okyeron/neotrellis-monome/enclosure/flexi-pcb3-1080.jpg

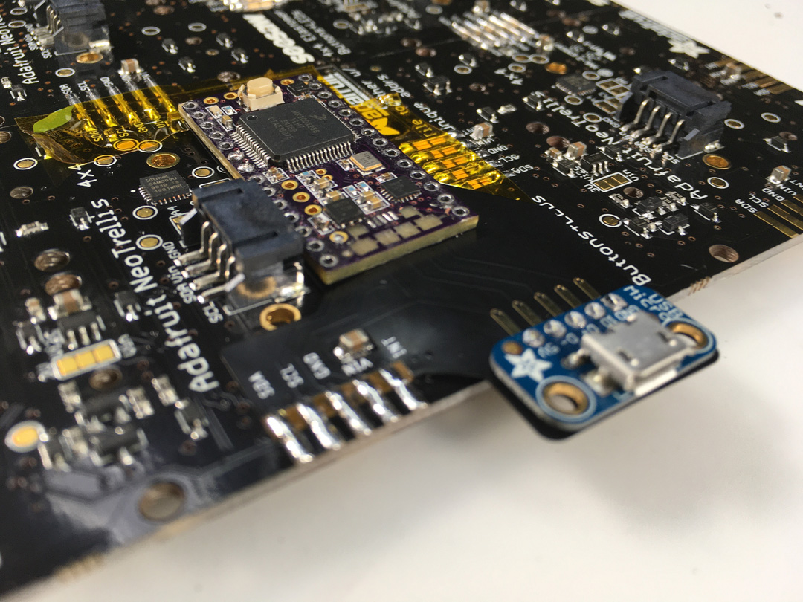
enclosure/flexi-pcb3-1080.jpg
