okyeron/neotrellis-monome/enclosure/IMG_2868.JPG

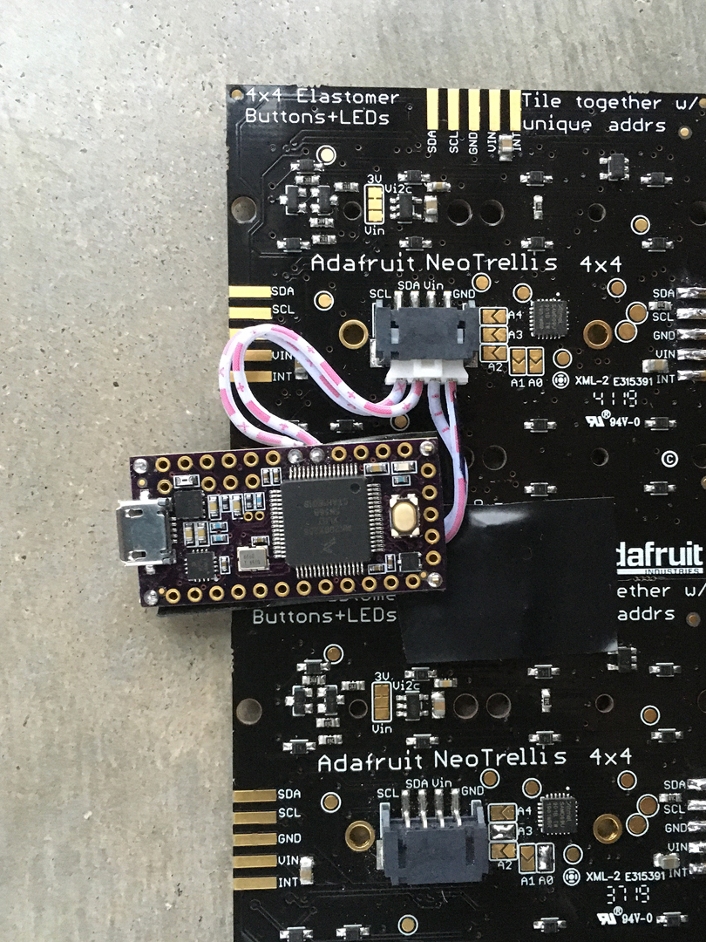
enclosure/IMG_2868.JPG
