okyeron/neotrellis-monome/enclosure/IMG_2871.JPG

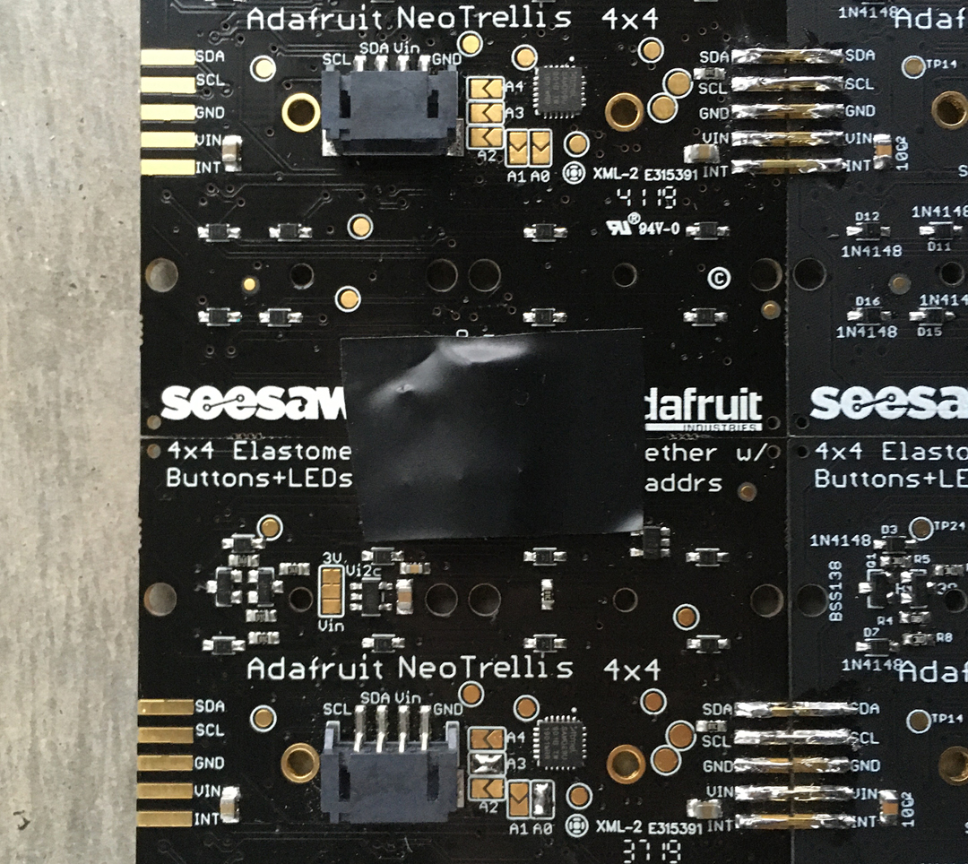
enclosure/IMG_2871.JPG
