okyeron/neotrellis-monome/enclosure/IMG_2872.JPG

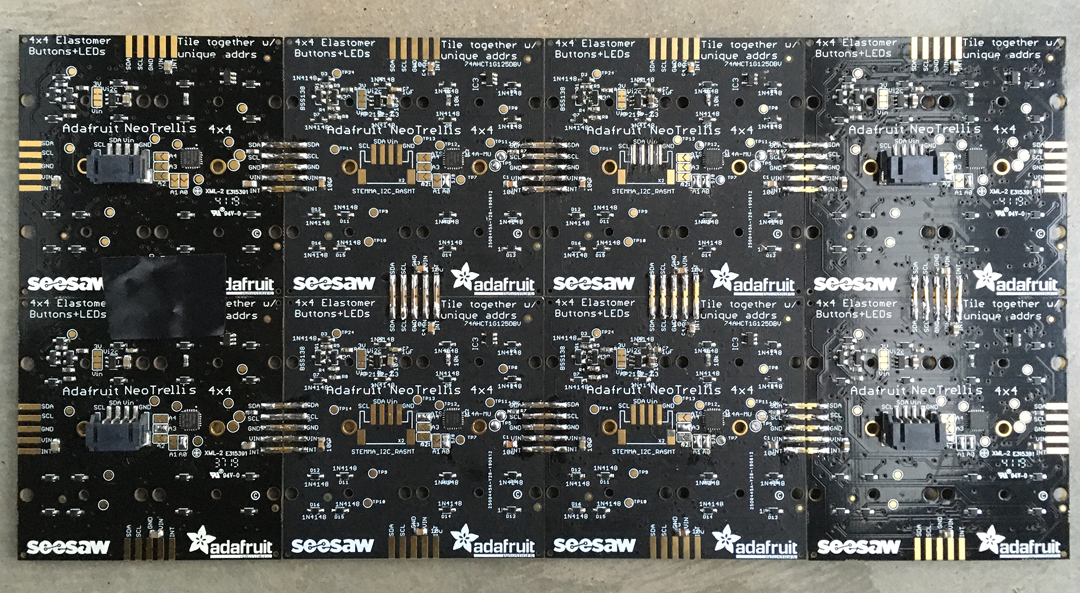
enclosure/IMG_2872.JPG
