okyeron/neotrellis-monome/enclosure/IMG_2873.JPG

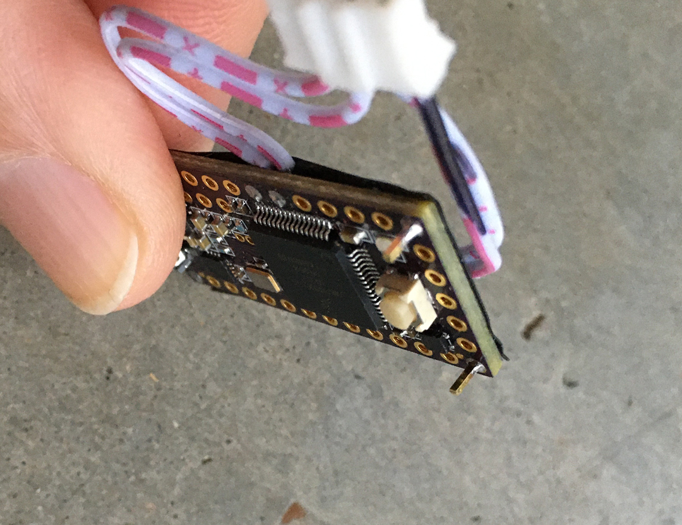
enclosure/IMG_2873.JPG
