okyeron/neotrellis-monome/enclosure/IMG_2874.JPG

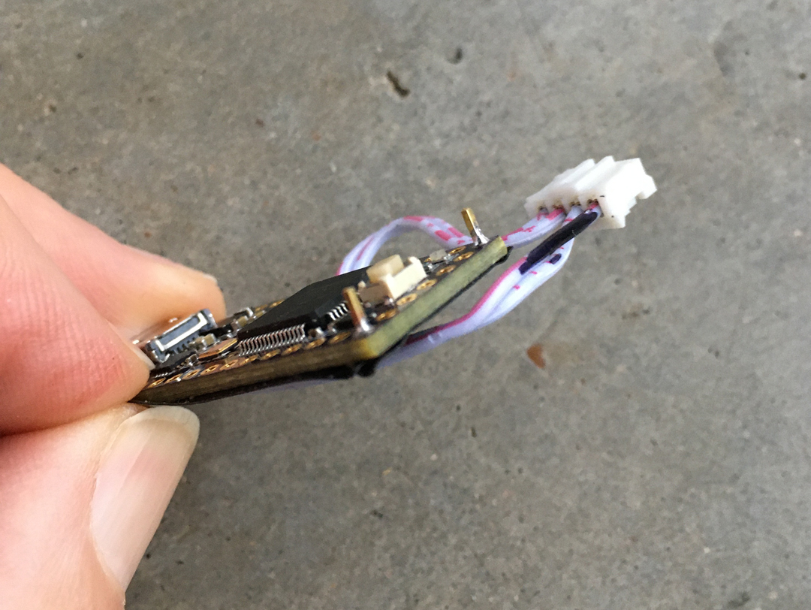
enclosure/IMG_2874.JPG
