okyeron/neotrellis-monome/enclosure/IMG_2875.JPG

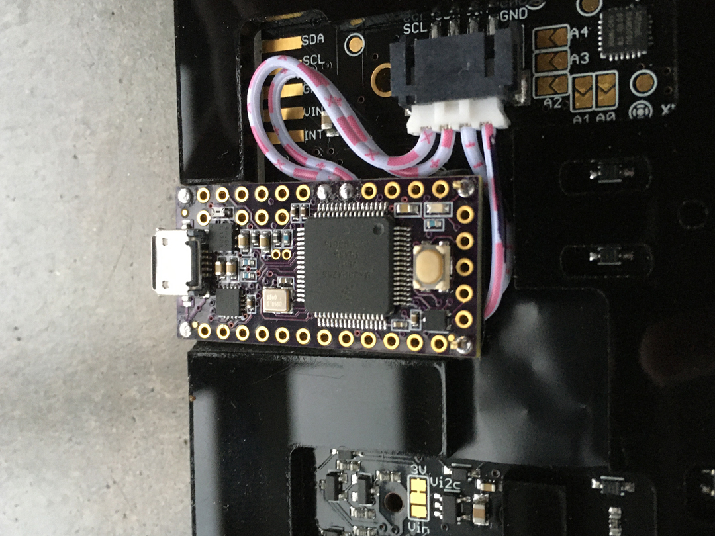
enclosure/IMG_2875.JPG
