okyeron/neotrellis-monome/enclosure/IMG_2876.JPG

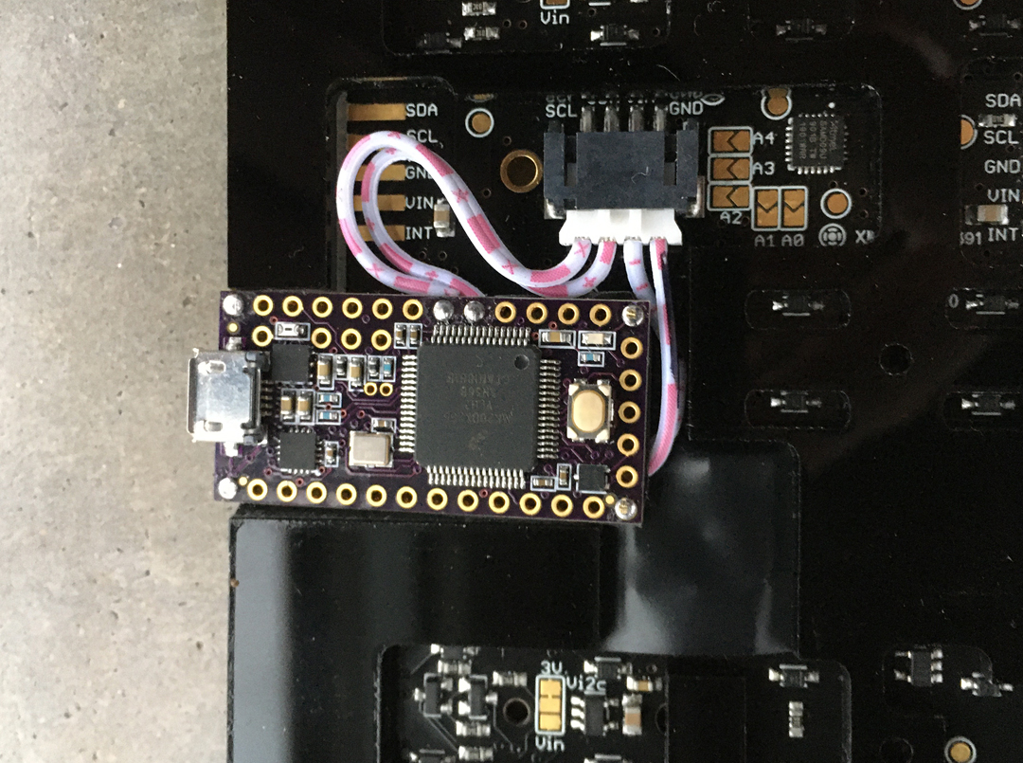
enclosure/IMG_2876.JPG
