okyeron/neotrellis-monome/enclosure/IMG_2877.JPG

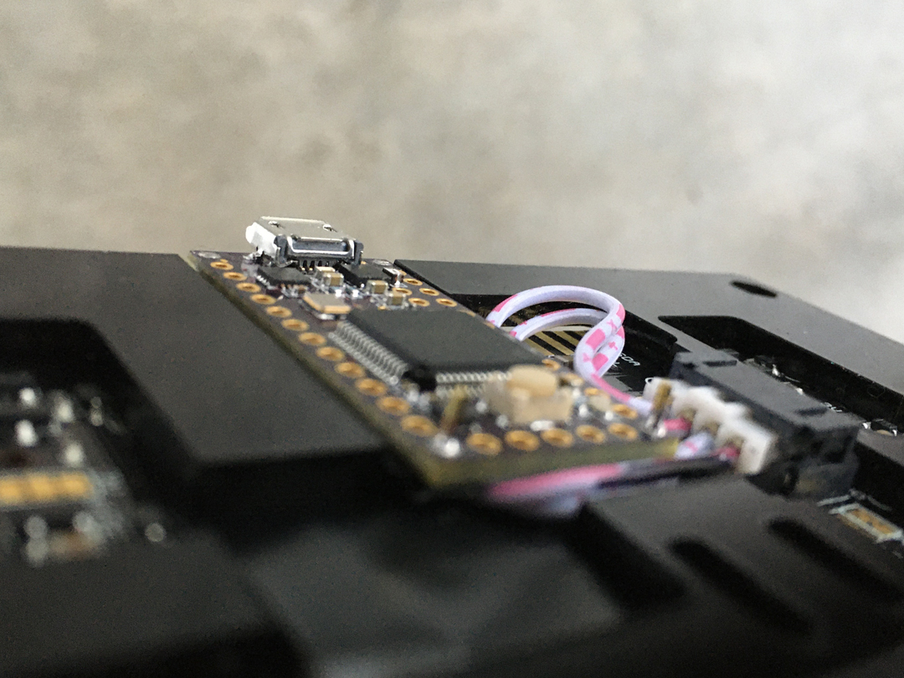
enclosure/IMG_2877.JPG
