okyeron/neotrellis-monome/enclosure/IMG_2879.JPG

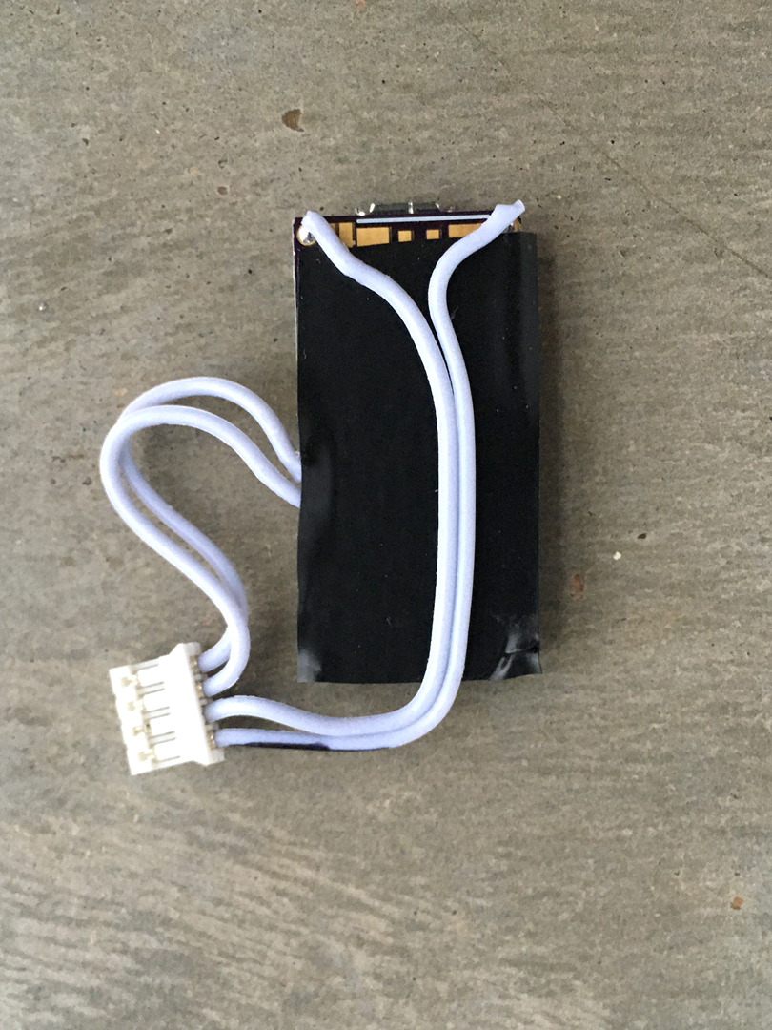
enclosure/IMG_2879.JPG
