okyeron/neotrellis-monome/enclosure/IMG_2880.JPG

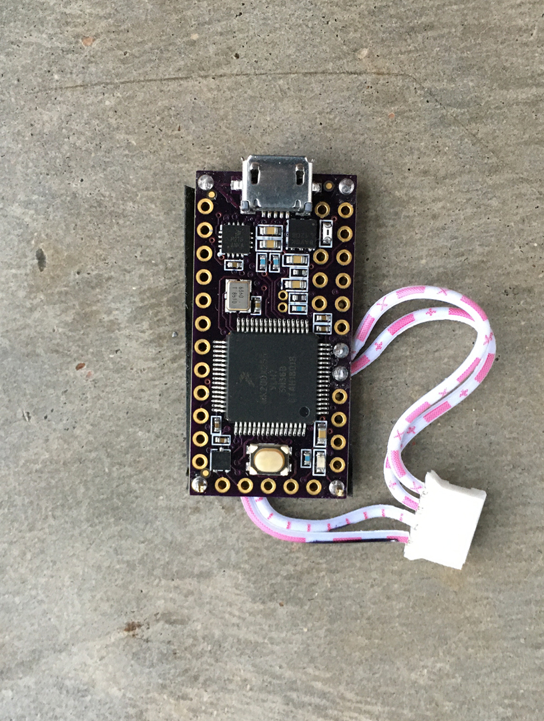
enclosure/IMG_2880.JPG
