okyeron/neotrellis-monome/neotrellis_monome_rp2040/src/debug.h

#ifndef DEBUG_H
#define DEBUG_H

#include <Arduino.h>

const int INFO = 1;
const int WARN = 2;
const int ERROR = 3;

const int DEBUG_LEVEL = INFO;

void debug(int level, const char *message);
void debug(int level, String message);

void debugln(int level, const char *message);
void debugln(int level, String message);
void debugln(int level);

void debugf(int level, const char *message, ...);
void debugf(int level, String message, ...);

void debugfln(int level, const char *message, ...);
void debugfln(int level, String message, ...);

#endif
